dymek84/ESP32-Led-Matrix-Clock/pictures/IMG_6875.jpeg

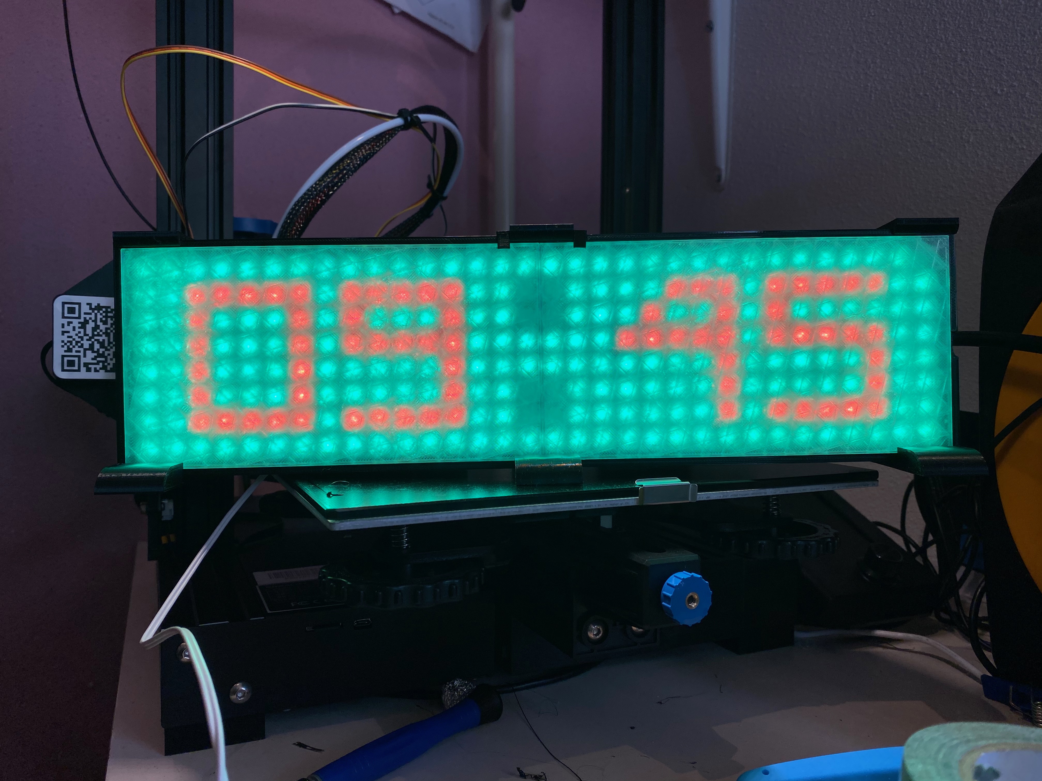
pictures/IMG_6875.jpeg
