dymek84/ESP32-Led-Matrix-Clock/src/MatrixDefs.h

#define XRES 32                                       // X RESOLUTION MATRIX
#define YRES 8                                        // Y RESOLUTION MATRIX
#include <map>

int ledArray[XRES * YRES] =                           // THIS WILL HOLD (DURING SETUP) THE MATRIX CONTAINING THE MAPPING OF LED NUMBER IN CORRECT ORDER VERSUS THE LED NUMBER ON MATRIX
{
  0, 15, 16, 31, 32, 47, 48, 63, 64, 79, 80, 95, 96, 111, 112, 127, 128, 143, 144, 159, 160, 175, 176, 191, 192, 207, 208, 223, 224, 239, 240, 255,
  1, 14, 17, 30, 33, 46, 49, 62, 65, 78, 81, 94, 97, 110, 113, 126, 129, 142, 145, 158, 161, 174, 177, 190, 193, 206, 209, 222, 225, 238, 241, 254,
  2, 13, 18, 29, 34, 45, 50, 61, 66, 77, 82, 93, 98, 109, 114, 125, 130, 141, 146, 157, 162, 173, 178, 189, 194, 205, 210, 221, 226, 237, 242, 253,
  3, 12, 19, 28, 35, 44, 51, 60, 67, 76, 83, 92, 99, 108, 115, 124, 131, 140, 147, 156, 163, 172, 179, 188, 195, 204, 211, 220, 227, 236, 243, 252,
  4, 11, 20, 27, 36, 43, 52, 59, 68, 75, 84, 91, 100, 107, 116, 123, 132, 139, 148, 155, 164, 171, 180, 187, 196, 203, 212, 219, 228, 235, 244, 251,
  5, 10, 21, 26, 37, 42, 53, 58, 69, 74, 85, 90, 101, 106, 117, 122, 133, 138, 149, 154, 165, 170, 181, 186, 197, 202, 213, 218, 229, 234, 245, 250,
  6, 9, 22, 25, 38, 41, 54, 57, 70, 73, 86, 89, 102, 105, 118, 121, 134, 137, 150, 153, 166, 169, 182, 185, 198, 201, 214, 217, 230, 233, 246, 249,
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
  {"O", 15},
  {"p", 16},
  {"P", 16},
  {"q", 17},
  {"Q", 17},
  {"R", 18},
  {"r", 18},
  {"S", 19},
  {"s", 19},
  {"T", 20},
  {"t", 20},
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
  {"@", 39}, // will show a heart
  {" ", 40},
  {"'", 41}, // will show a degree
  {"%", 42}, // arrow down
  {"^", 43}, //arrow up
  {":", 0}
};
